RetroScaler/RP2040-PICO-BOOT/PCB 3D MAP/20221014101708.jpg

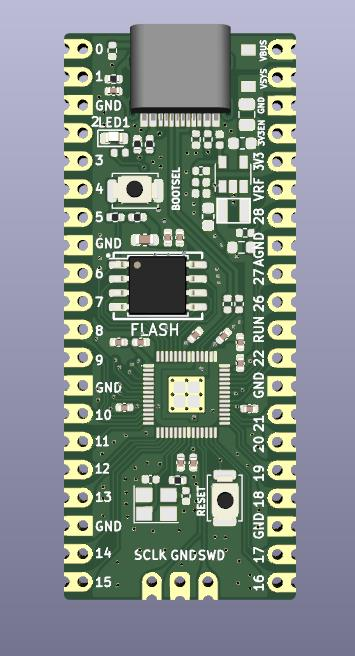
PCB 3D MAP/20221014101708.jpg
