RetroScaler/RP2040-PICO-BOOT/PCB 3D MAP/20221018144731.jpg

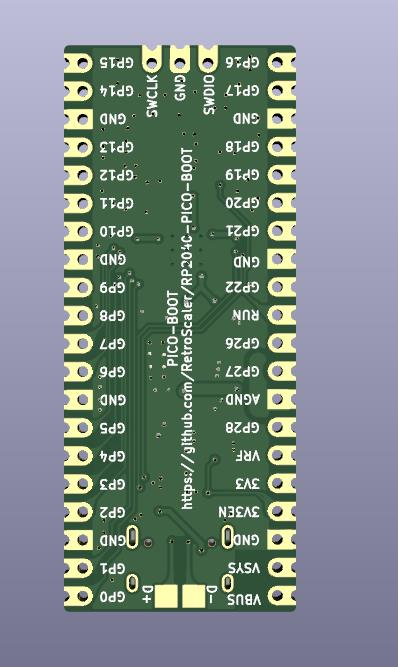
PCB 3D MAP/20221018144731.jpg
